fabiobaltieri/spotlight/firmware/src/state.h

#include <stdint.h>

enum {
	MODE_STANDBY = 0,
	MODE_MANUAL = 1,
	MODE_AUTO = 2,
	MODE_SHUTDOWN = 0xf,
};

enum {
	LEVEL_OFF = 0,
	LEVEL_LOW = 1,
	LEVEL_MEDIUM = 2,
	LEVEL_HIGH = 3,
	LEVEL_BEAM = 4,
	NUM_LEVELS = 5,
};

struct state {
	uint8_t mode;
	uint8_t level;
	uint16_t batt_mv;
	uint8_t soc;
	int8_t temp;
	uint8_t tte;
	uint8_t dc;
};

extern struct state state;
